SteveMayze/coaxTester/doc/IMG359.jpg

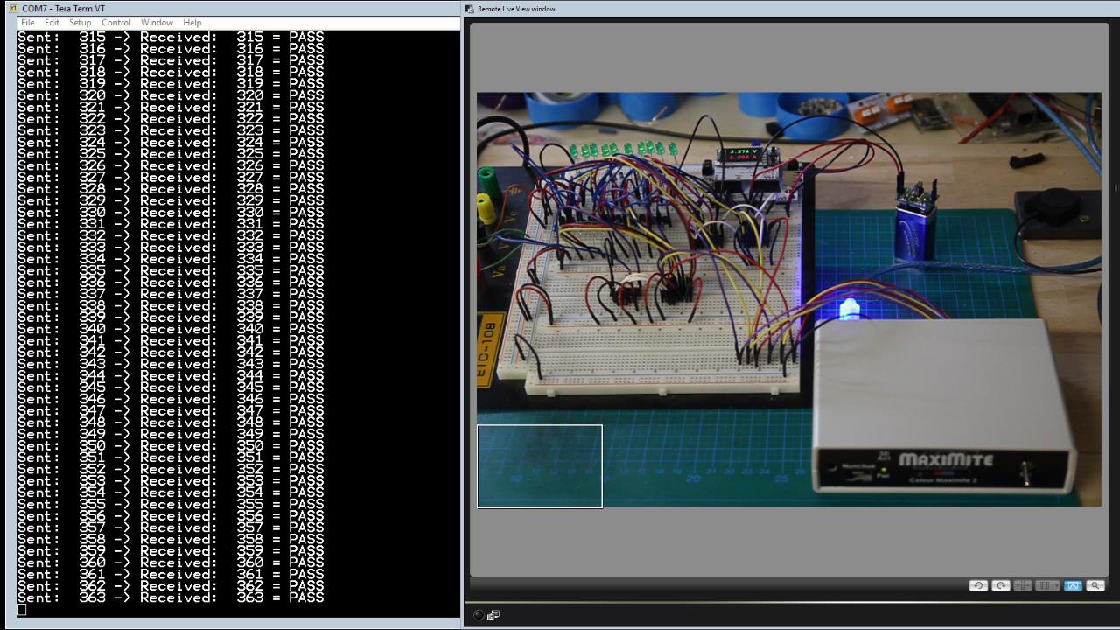
doc/IMG359.jpg
