SteveMayze/coaxTester/doc/FB-EPG.pdf

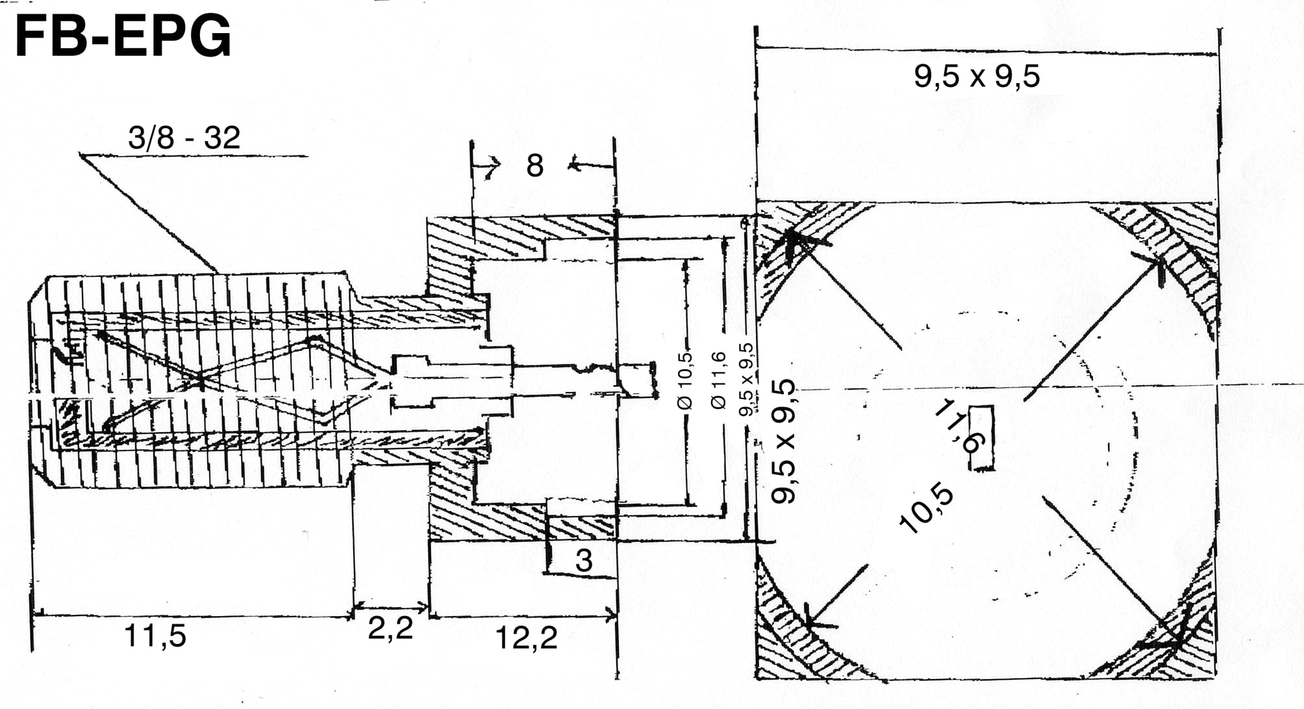
[picture p3: page 1]
