SteveMayze/coaxTester/doc/74ls138_Application.png

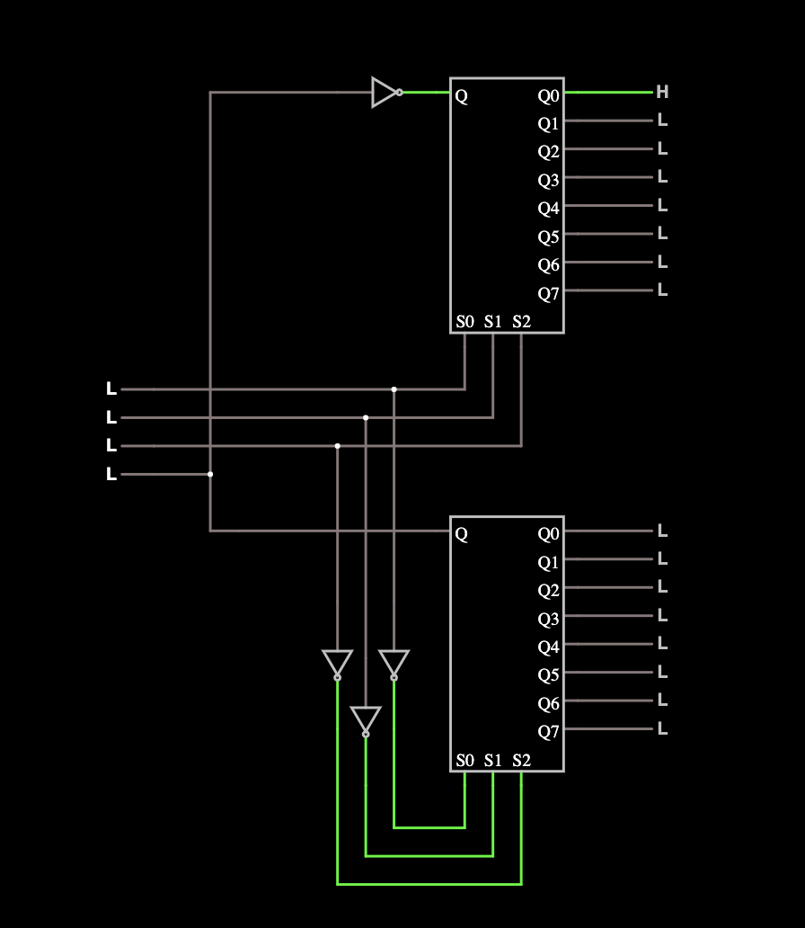
doc/74ls138_Application.png
