SteveMayze/coaxTester/doc/74ls138_TruthTable.png

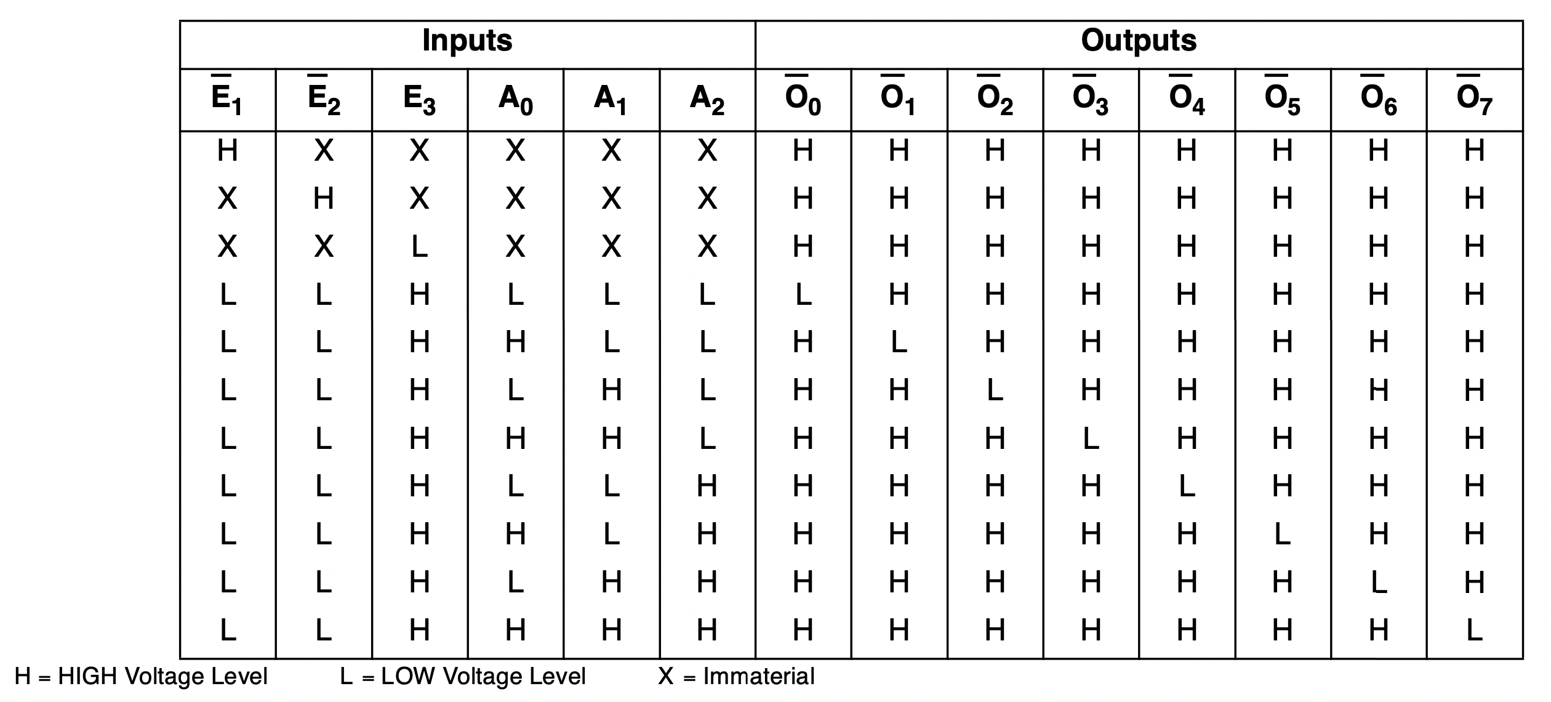
doc/74ls138_TruthTable.png
