SteveMayze/coaxTester/doc/74ls138Connection.png

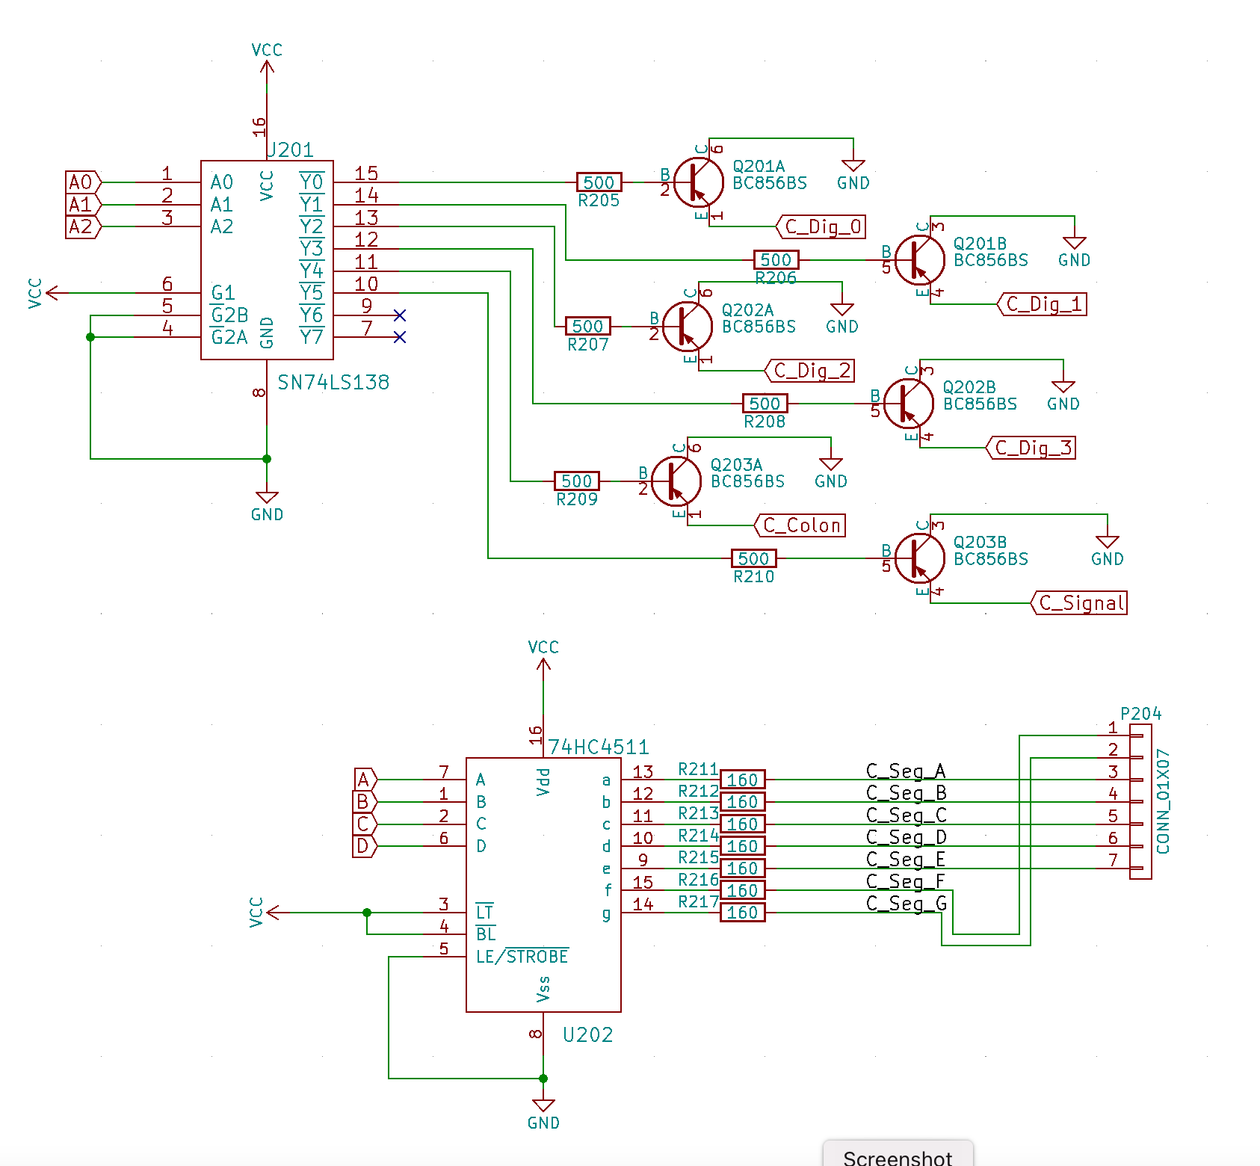
doc/74ls138Connection.png
