SteveMayze/coaxTester/doc/4532_Applicaiton.png

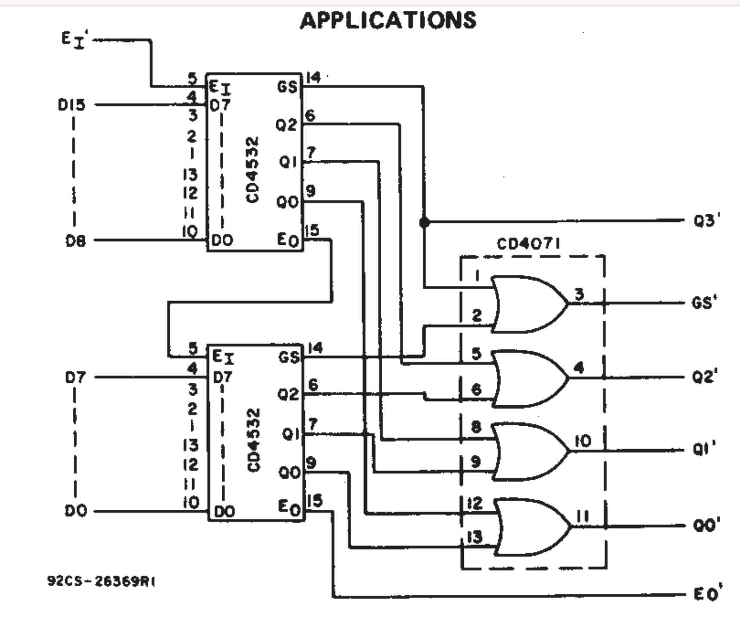
doc/4532_Applicaiton.png
