SteveMayze/coaxTester/doc/4532_TruthTable.png

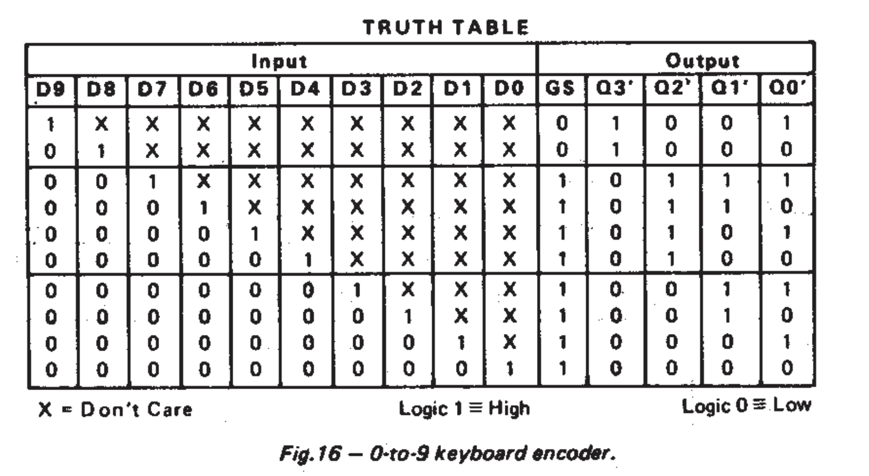
doc/4532_TruthTable.png
