SteveMayze/coaxTester/doc/Cascading_74LS138.png

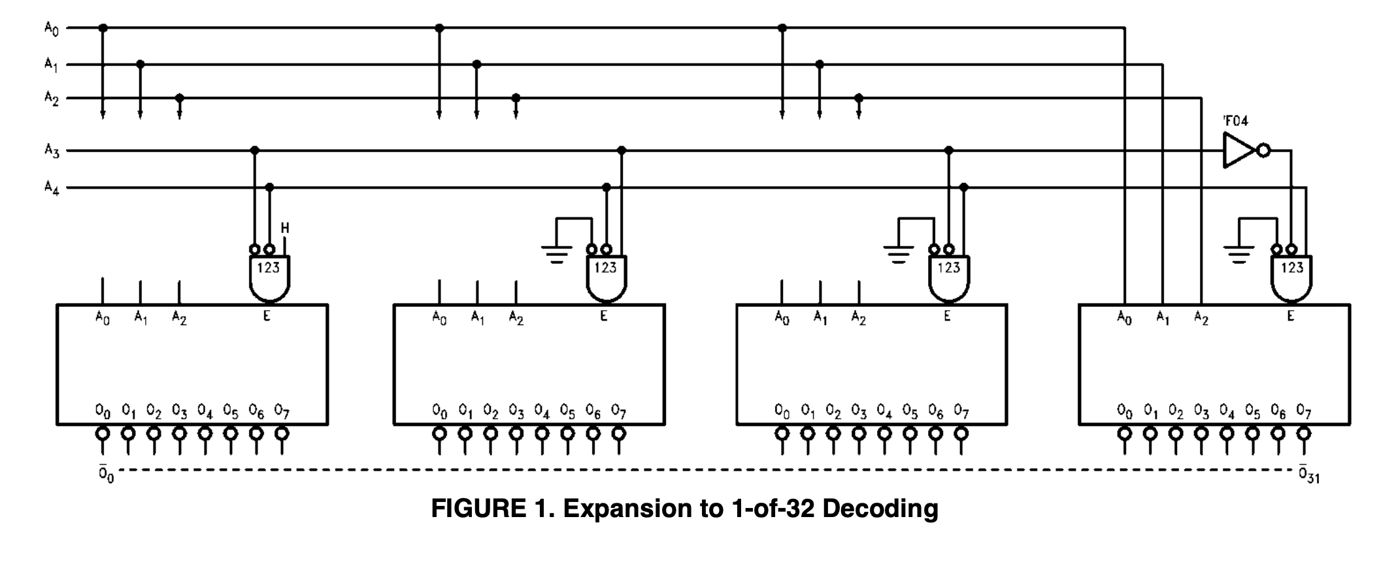
doc/Cascading_74LS138.png
