SteveMayze/coaxTester/doc/encoder-decoder-input.png

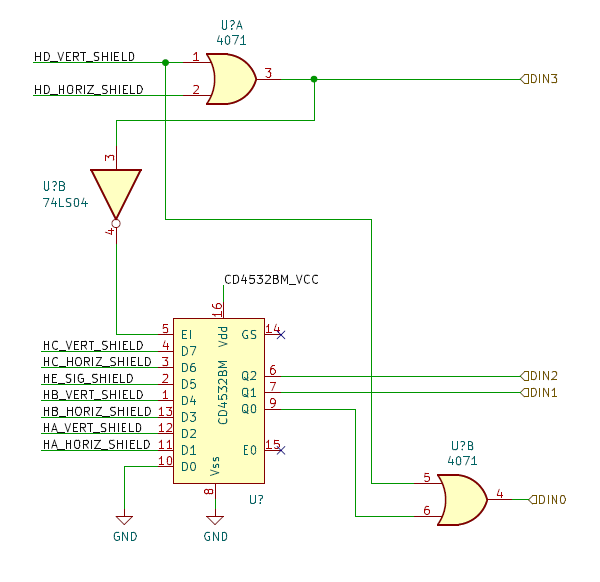
doc/encoder-decoder-input.png
