SteveMayze/coaxTester/doc/encoder-decoder-output.png

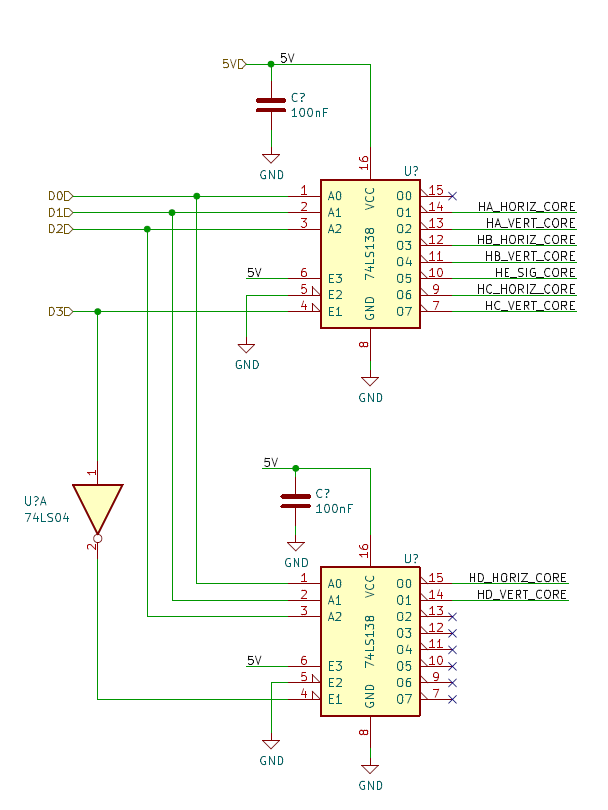
doc/encoder-decoder-output.png
