SteveMayze/coaxTester/doc/shift-registers-in.png

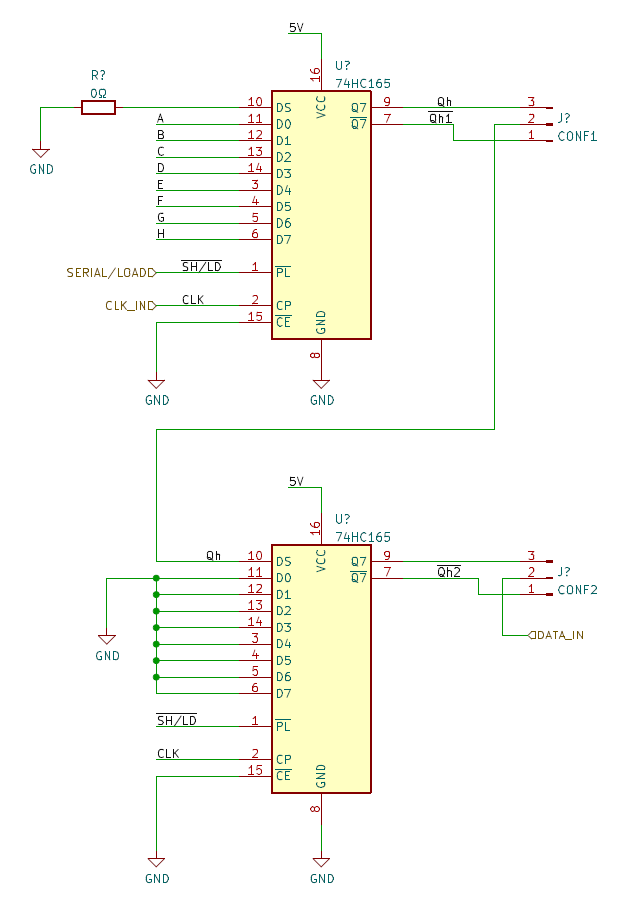
doc/shift-registers-in.png
