SteveMayze/coaxTester/doc/shift-registers-out.png

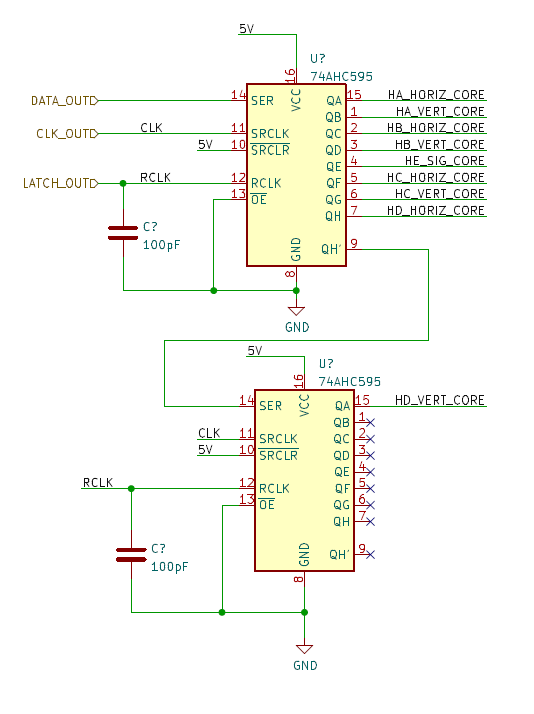
doc/shift-registers-out.png
