SteveMayze/coaxTester/freecad/eadogm128/EA DOGM128.JPG

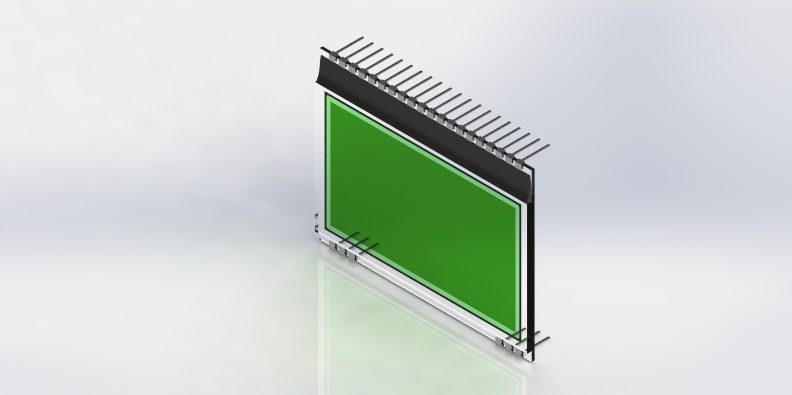
freecad/eadogm128/EA DOGM128.JPG
