SteveMayze/coaxTester/doc/CoaxTester Context.png

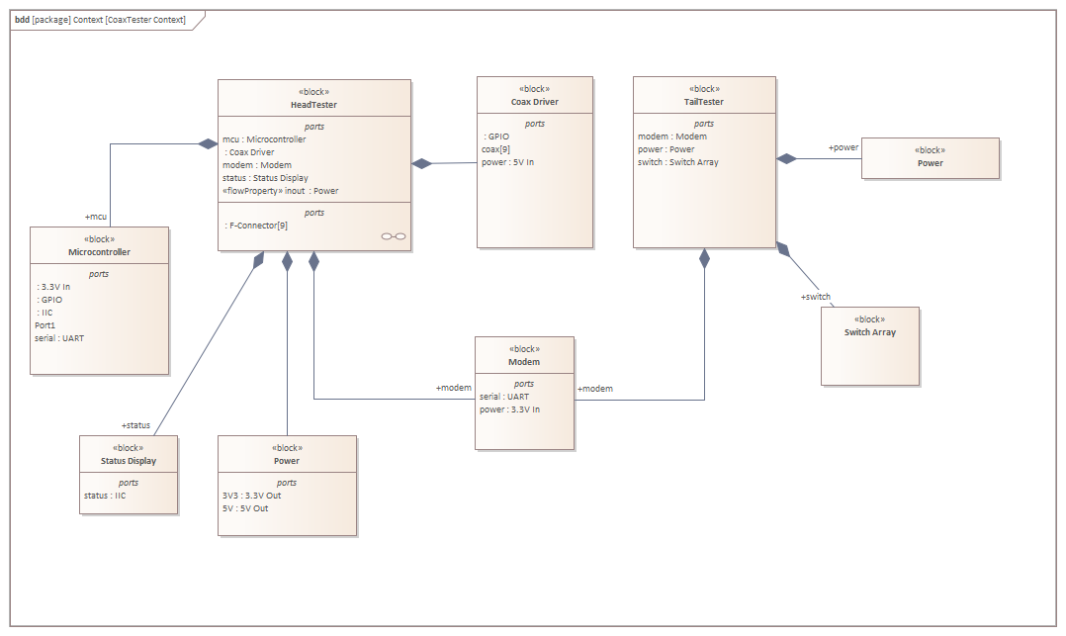
doc/CoaxTester Context.png
